mhoyer/hushbox-control/native/src/TempReader/TempReader.cpp

#define REQUIRESALARMS false
#include <DallasTemperature.h>

#include "./TempReader/TempReader.h"

OneWire *oneWire;
DallasTemperature *sensors;
DeviceAddress in_sensor, out_sensor;

void temp_setup(uint8_t pin)
{
    oneWire = new OneWire(pin);
    sensors = new DallasTemperature(oneWire);
    sensors->begin();

    Serial.print("Found ");
    Serial.print(sensors->getDeviceCount(), DEC);
    Serial.print(" devices on pin ");
    Serial.print(pin);
    Serial.println(".");

    // search for devices on the bus and assign based on an index.
    if (!sensors->getAddress(in_sensor, 0))
        Serial.println("Unable to find address for Device 0");
    if (!sensors->getAddress(out_sensor, 1))
        Serial.println("Unable to find address for Device 1");
}

temp_values_t _recent_temp_values;
temp_values_t temp_read()
{
    sensors->requestTemperatures();
    _recent_temp_values.in = sensors->getTempC(in_sensor);
    _recent_temp_values.out = sensors->getTempC(out_sensor);
    return _recent_temp_values;
}
